introlab/MOvIT-Detect-Hardware/MOvIT CAD/MainUnit_RaspberryPI4/pieces_2_print/RPI4_Canakit_cover_battery_protector.stl

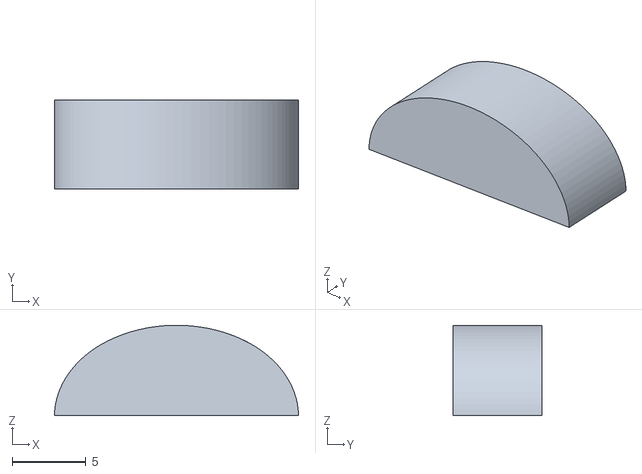
[picture p16: CAD file, 2020-08-28]
MOvIT CAD/MainUnit_RaspberryPI4/pieces_2_print/RPI4_Canakit_cover_battery_protector.stl
16.5 x 6.00 x 6.12
