introlab/MOvIT-Detect-Hardware/MOvIT CAD/MainUnit_RaspberryPI4/raspberry-pi-4-model/2X USB2.0 PORTS, RPi4ModelB.SLDPRT

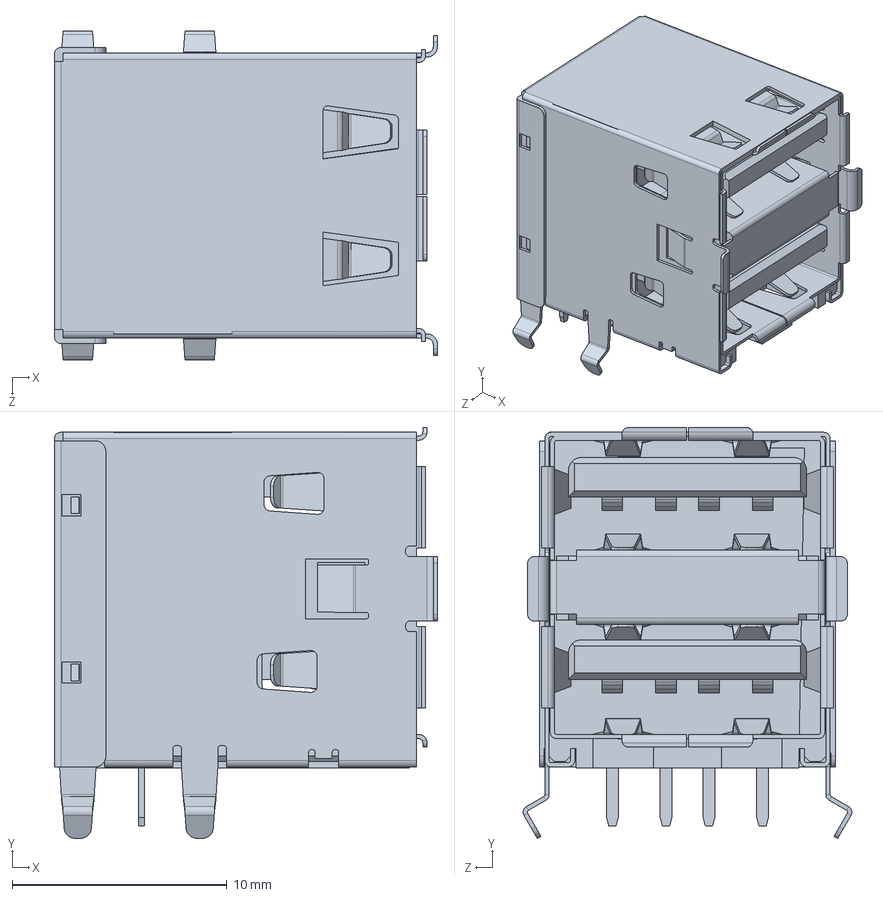
[picture p17: CAD file, 2020-08-28]
MOvIT CAD/MainUnit_RaspberryPI4/raspberry-pi-4-model/2X USB2.0 PORTS, RPi4ModelB.SLDPRT
17.9 x 19.2 x 15.3 mm
