introlab/MOvIT-Detect-Hardware/MOvIT CAD/MainUnit_RaspberryPI4/RPI4_Canakit_Case.STEP

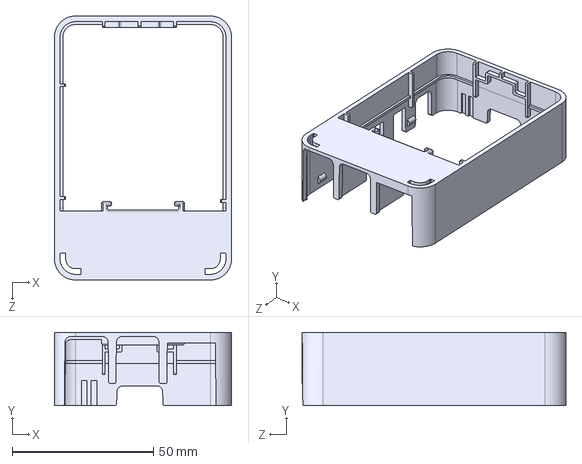
[picture p18: CAD file, 2020-08-28]
MOvIT CAD/MainUnit_RaspberryPI4/RPI4_Canakit_Case.STEP
62.8 x 26.0 x 93.5 mm
