introlab/MOvIT-Detect-Hardware/MOvIT CAD/MainUnit_RaspberryPI4/pieces_2_print/RPI4_Canakit_cover_clip_down_plain.STL

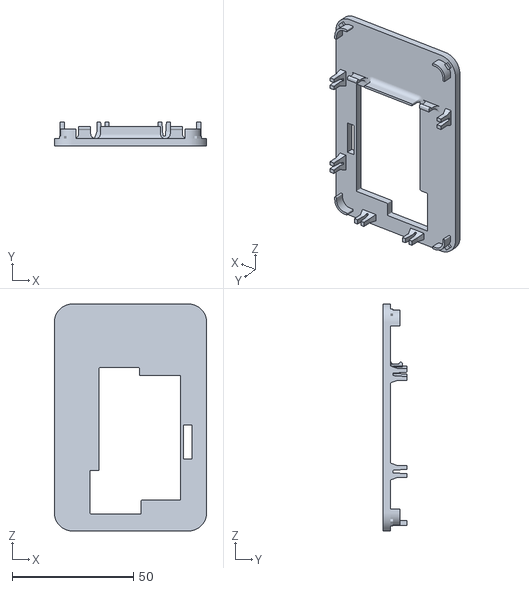
[picture p19: CAD file, 2020-08-28]
MOvIT CAD/MainUnit_RaspberryPI4/pieces_2_print/RPI4_Canakit_cover_clip_down_plain.STL
62.7 x 9.80 x 93.5
