introlab/MOvIT-Detect-Hardware/MOvIT CAD/MainUnit_RaspberryPI4/raspberry-pi-4-model/Broadcom BCM54213PE Gigabit Ethernet Transceiver, RPi4ModelB.SLDPRT

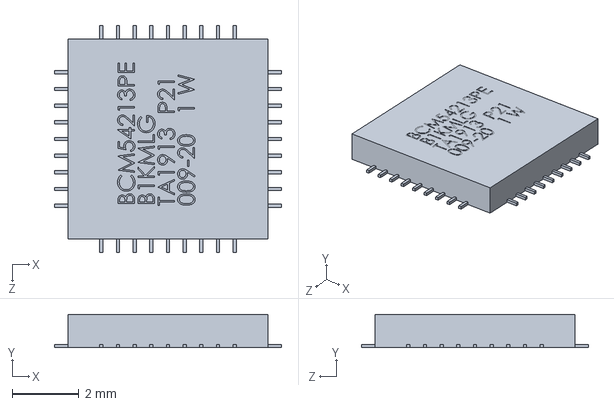
[picture p20: CAD file, 2020-08-28]
MOvIT CAD/MainUnit_RaspberryPI4/raspberry-pi-4-model/Broadcom BCM54213PE Gigabit Ethernet Transceiver, RPi4ModelB.SLDPRT
6.80 x 1.00 x 6.80 mm
