introlab/MOvIT-Detect-Hardware/MOvIT CAD/MainUnit_RaspberryPI4/raspberry-pi-4-model/2X USB3.0 PORTS, RPi4ModelB.SLDPRT

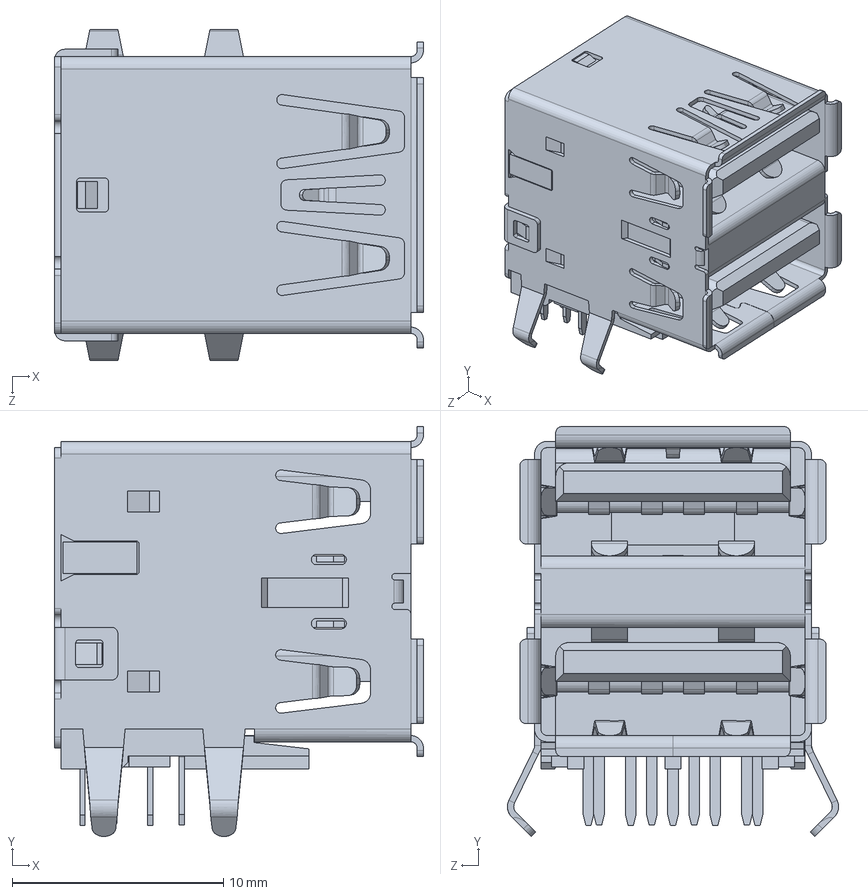
[picture p21: CAD file, 2020-08-28]
MOvIT CAD/MainUnit_RaspberryPI4/raspberry-pi-4-model/2X USB3.0 PORTS, RPi4ModelB.SLDPRT
17.5 x 19.4 x 15.7 mm
