introlab/MOvIT-Detect-Hardware/MOvIT CAD/MainUnit_RaspberryPI4/raspberry-pi-4-model/2.54 mm DUPONT MALE PIN HEADER, POE, 2X2, RPi4ModelB.SLDPRT

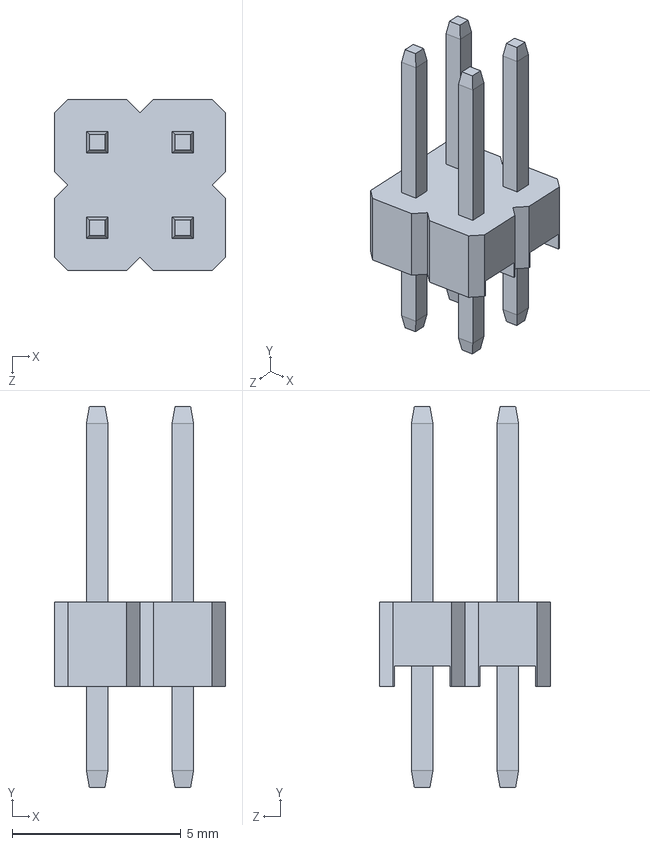
[picture p22: CAD file, 2020-08-28]
MOvIT CAD/MainUnit_RaspberryPI4/raspberry-pi-4-model/2.54 mm DUPONT MALE PIN HEADER, POE, 2X2, RPi4ModelB.SLDPRT
5.08 x 11.3 x 5.08 mm
