introlab/MOvIT-Detect-Hardware/MOvIT CAD/MainUnit_RaspberryPI4/raspberry-pi-4-model/Microphone Plug, RPi4ModelB.SLDPRT

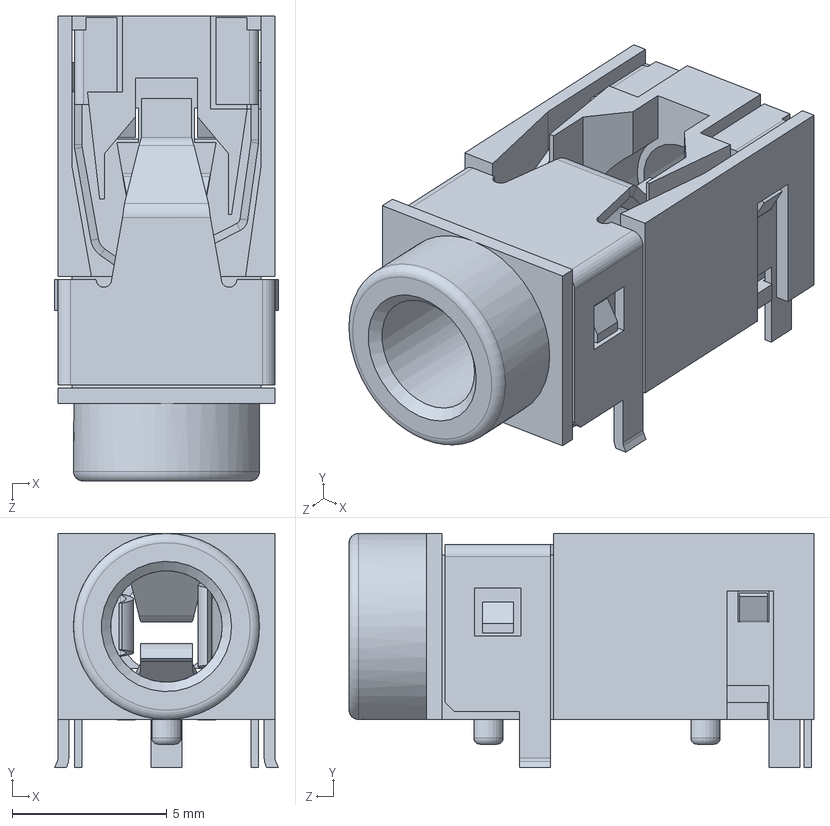
[picture p23: CAD file, 2020-08-28]
MOvIT CAD/MainUnit_RaspberryPI4/raspberry-pi-4-model/Microphone Plug, RPi4ModelB.SLDPRT
7.23 x 7.55 x 15.0 mm
